Juani005999/ROMV2/sources/ROMV2/src/ROMV2_APP.cpp

#include <ROMV2_APP.h>

/// <summary>
/// Constructeur
/// </summary>
ROMV2_APP::ROMV2_APP()
{
}

/// <summary>
/// Initialisation des capteurs propres au modèle complet.
/// </summary>
void ROMV2_APP::InitModelSensors()
{
	// Initialisation des membres
	_tft = new ROMV2_TFT();

	// Initiaisation du type d'application en cours
	_appType = APP_ROMV2;

	// Initialisation des objets représentant les capteurs et périphériques
	_tft->Init(_appType, &_dataEnvironment, &_dataLuminosity, &_dataSkyState, &_dataAcceleration, &_dataGPS, &_dataWifi, &_dataMqtt, &_bluetoothConnected, &_networkMode);
	_bme280.Init(&_dataEnvironment);
	_tsl2591.Init(_tft, &_dataLuminosity, &_dataEnvironment);
	_mlx90614.Init(&_dataSkyState);
	_adxl345.Init(&_dataAcceleration);
	_gps.Init(&_dataGPS);
	if (_networkMode == NETWORK_BLE)
	{
		_bluetoothLE.Init(_appType, &_bluetoothConnected, &_dataEnvironment, &_dataLuminosity, &_dataSkyState);
	}
	if (_networkMode == NETWORK_WIFI)
	{
		_wifi.Init(_appType, &_dataWifi, &_dataMqtt);
		_mqtt.Init(_appType, &_dataWifi, &_dataMqtt, &_dataEnvironment, &_dataLuminosity, &_dataSkyState, &_dataAcceleration, &_dataGPS);
	}
}

/// <summary>
/// Lectures cadencées des capteurs propres au modèle complet.
/// </summary>
void ROMV2_APP::LoopModelSensors()
{
	// Lecture température, humidité, pression atm. et point de rosée
	_bme280.ReadEnvironment();

	// Lecture Luminosité
	_tsl2591.ReadLuminosity();

	// Lecture Température IR
	_mlx90614.ReadIRTemp();

	// Lecture Accélération uniquement si l'affichage courant est DISPLAY_ACCELERATION
	// Sur l'écran niveau à bulle : on suspend la lecture TSL pour libérer le bus I2C à l'ADXL.
	if (_currentDisplayScreenType == DISPLAY_ACCELERATION)
	{
		_tsl2591.SetReadingPaused(true);
		_adxl345.ReadAcceleration();
	}
	else
	{
		_tsl2591.SetReadingPaused(false);
	}

	// Lecture des données GPS et vérification de l'état du GPS
	_gps.ReadGPS();
	_gps.CheckGPSState();
}

/// <summary>
/// Lecture de l'état du Joystick
/// </summary>
void ROMV2_APP::ReadJoystickState()
{
	// Lecture de l'état du Joystick sur intervalle
	if (millis() > _chronoReadJoystick + JOYSTICK_READ_INTERVAL)
	{
		bool addChronoInterval = true;

		// Bouton du Joystick
		if (digitalRead(JOYSTICK_PIN_SWITCH) == LOW)
		{
			// Actualisation Chrono et Flag
			if (!_joystickPressed)
			{
				_chronoJoystickButtonPressed = millis();
			}
			_joystickPressed = true;

			// Clic long
			if (millis() > _chronoJoystickButtonPressed + JOYSTICK_BUTTON_LONG_INTERVAL)
			{
				_currentAction = ACTION_CLICK_LONG;
				// Actualisation des Flags
				_joystickPressed = false;
				// Trace
				debugln(F(""));
				debugln(F("[ACTION] Long Click"));
			}
		}
		// Pour le bouton Joystick, on traite le clic court sur relachement du bouton
		else
		{
			if (_joystickPressed && _currentDisplayScreenType != DISPLAY_NONE)
			{
				_currentAction = ACTION_CLICK;
				debugln(F(""));
				debugln(F("[ACTION] Click"));
			}
			// Actualisation des Flags
			_joystickPressed = false;
		}

		// Position du Joystick :
		// - Pas de lecture si le bouton du Joystick est pressé, afin de réduire les miss clicks
		if (!_joystickPressed)
		{
			int x = analogRead(JOYSTICK_PIN_X);
			int y = analogRead(JOYSTICK_PIN_Y);

			if (y > ROMV2_JOYSTICK_POSITION_MIN_VALUE_HIGH && !_joystickMoved)
			{
				_joystickMoved = true;
				_currentAction = ACTION_RIGHT;
				debugln(F(""));
				debugln(F("[ACTION] Right"));
			}
			else if (y < ROMV2_JOYSTICK_POSITION_MIN_VALUE_LOW && !_joystickMoved)
			{
				_joystickMoved = true;
				_currentAction = ACTION_LEFT;
				debugln(F(""));
				debugln(F("[ACTION] Left"));
			}
			else if (x > ROMV2_JOYSTICK_POSITION_MIN_VALUE_HIGH)
			{
				// Update des commandes uniquement si pas de mouvement en cours
				if (!_joystickMoved)
				{
					_currentAction = ACTION_UP;
					_joystickMoved = true;
					_chronoJoystickButtonMoved = millis();

					// Trace
					debugln(F(""));
					debugln(F("[ACTION] Up"));
				}
				// Sur l'écran Calibration et sur mouvement long, on update l'Action en cours afin d'accélérer la décrémentation
				if (_currentDisplayScreenType == DISPLAY_TSL2591_CALIBRATION && millis() > _chronoJoystickButtonMoved + JOYSTICK_MOVE_LONG_INTERVAL)
				{
					_currentAction = ACTION_UP;
					_chronoJoystickButtonMoved += 50;
					addChronoInterval = false;

					// Trace
					debugln(F(""));
					debugln(F("[ACTION] Up"));
				}
			}
			else if (x < ROMV2_JOYSTICK_POSITION_MIN_VALUE_LOW)
			{
				// Update des commandes uniquement si pas de mouvement en cours
				if (!_joystickMoved)
				{
					_currentAction = ACTION_DOWN;
					_joystickMoved = true;
					_chronoJoystickButtonMoved = millis();

					// Trace
					debugln(F(""));
					debugln(F("[ACTION] Down"));
				}
				// Sur l'écran Calibration et sur mouvement long, on update l'Action en cours afin d'accélérer l'incrémentation
				if (_currentDisplayScreenType == DISPLAY_TSL2591_CALIBRATION && millis() > _chronoJoystickButtonMoved + JOYSTICK_MOVE_LONG_INTERVAL)
				{
					_currentAction = ACTION_DOWN;
					_chronoJoystickButtonMoved += 50;
					addChronoInterval = false;

					// Trace
					debugln(F(""));
					debugln(F("[ACTION] Down"));
				}
			}
			else
			{
				if (x < ROMV2_JOYSTICK_POSITION_MIN_VALUE_HIGH
					&& x > ROMV2_JOYSTICK_POSITION_MIN_VALUE_LOW
					&& y < ROMV2_JOYSTICK_POSITION_MIN_VALUE_HIGH
					&& y > ROMV2_JOYSTICK_POSITION_MIN_VALUE_LOW)
				{
					_joystickMoved = false;
					_chronoJoystickButtonMoved = millis();
				}
			}
		}

		// Si une action est en cours, on force la mise à jour complète de l'affichage
		if (_currentAction != ACTION_NONE)
		{
			if (_currentDisplayScreenType != DISPLAY_TSL2591_CALIBRATION
				|| (_currentAction != ACTION_UP && _currentAction != ACTION_DOWN))
			{
				_tft->ForceRedraw();
			}
		}

		// Actualisation Chrono et Flag
		if (addChronoInterval)
		{
			_chronoReadJoystick = millis();
		}
	}
}

/// <summary>
/// Ordre complet des écrans navigables au joystick pour le modèle ROMV2.
/// L'écran WiFi reste filtré à l'exécution par IsScreenVisible (présent seulement en mode WiFi).
/// </summary>
const DISPLAY_SCREEN_TYPE* ROMV2_APP::GetScreenOrder(uint8_t& count) const
{
	static const DISPLAY_SCREEN_TYPE order[] =
	{
		DISPLAY_HOME,
		DISPLAY_LUX,
		DISPLAY_ENVIRONMENT,
		DISPLAY_IRTEMP,
		DISPLAY_ACCELERATION,
		DISPLAY_GPS,
		DISPLAY_NETWORK,
		DISPLAY_WIFI,
		DISPLAY_TSL2591_CALIBRATION
	};

	count = sizeof(order) / sizeof(order[0]);
	return order;
}
